an-dr-eas-k/the-alarm-clock/src/core/infrastructure/rpi_gpio.py

from concurrent.futures import ThreadPoolExecutor
import logging
import threading
from core.infrastructure.event_bus import EventBus
from core.infrastructure.events_infrastructure import (
    ButtonDirection,
    DeviceName,
    HwButtonEvent,
    HwButtonLongPressEvent,
    HwRotaryEvent,
    RotaryDirection,
)

LONG_PRESS_DURATION: float = 1.5  # seconds

logger = logging.getLogger("tac.core.infrastructure.rpi_gpio")

rotary_encoder_press_gpio: int = 5
rotary_encoder_a_gpio: int = 6
rotary_encoder_b_gpio: int = 13
mode_button_gpio: int = 12
invoke_button_gpio: int = 1


class RPiGPIOManager:

    executor: ThreadPoolExecutor
    gpio_callbacks = {}

    @property
    def _gpio_module(self):
        from RPi import GPIO  # type: ignore

        return GPIO

    def __init__(self, executor: ThreadPoolExecutor):
        self.executor = executor
        self.gpio_callbacks = {}

    def add_callback(self, pin_num, callback):
        self.gpio_callbacks[pin_num] = callback

    def setup(self):
        self._gpio_module.setmode(self._gpio_module.BCM)
        configured_pins = self.gpio_callbacks.keys()
        logger.info(f"Configuring gpio pins: {configured_pins}")

        for pin in configured_pins:
            self._gpio_module.setup(
                pin, self._gpio_module.IN, pull_up_down=self._gpio_module.PUD_UP
            )

            self._gpio_module.add_event_detect(
                pin,
                self._gpio_module.BOTH,
                callback=self.callback_wrapper,
                bouncetime=2,
            )

    def callback_wrapper(self, channel):
        all_pin_values = self.read_all_pins()
        logger.debug(
            f"GPIO event detected on channel {channel}, pin values: {all_pin_values}"
        )
        self.executor.submit(
            self.gpio_callbacks[channel],
            bool(all_pin_values[channel]),
            all_pin_values,
        )

    def read_all_pins(self):
        pin_values = {}
        for pin in self.gpio_callbacks.keys():
            pin_values[pin] = int(self._gpio_module.input(pin))
        return pin_values

    def cleanup(self):
        logger.info("Cleaning up GPIO")
        self._gpio_module.cleanup()


class GPIOInputManager:
    last_states = [(0, 0), (0, 0)]

    def __init__(self, gpio_manager: RPiGPIOManager, event_bus: EventBus = None):
        super().__init__()
        self.gpio_manager = gpio_manager
        self.event_bus = event_bus
        self._long_press_timers: dict[DeviceName, threading.Timer] = {}

        self.gpio_manager.add_callback(mode_button_gpio, self._mode_button_callback)
        self.gpio_manager.add_callback(invoke_button_gpio, self._invoke_button_callback)
        self.gpio_manager.add_callback(
            rotary_encoder_a_gpio, self._rotary_encoder_callback
        )
        self.gpio_manager.add_callback(rotary_encoder_b_gpio, lambda v, p: {})

        self.gpio_manager.setup()

        channel_a_value = int(
            not self.gpio_manager.read_all_pins()[rotary_encoder_a_gpio]
        )
        channel_b_value = int(
            not self.gpio_manager.read_all_pins()[rotary_encoder_b_gpio]
        )

        self.last_states = [(channel_a_value, channel_b_value), (None, None)]

        logger.info(
            f"gpio initialized for buttons and rotary encoder input. Initial rotary encoder state: {self.last_states[0]}"
        )

    def _rotary_encoder_callback(self, _: bool, pin_values=None):

        channel_a_value = pin_values[rotary_encoder_a_gpio]

        channel_b_value = pin_values[rotary_encoder_b_gpio]
        state = (channel_a_value, channel_b_value)
        logger.debug(
            f"Rotary encoder current state: {state}, last state: {self.last_states[0]}"
        )

        if channel_b_value != channel_a_value:
            logger.debug(
                f"Rotary clockwise detected, {'1st tick' if channel_a_value == 1 else 'later tick'}"
            )

            self.event_bus.emit(
                HwRotaryEvent(
                    DeviceName.ROTARY_ENCODER,
                    RotaryDirection.CLOCKWISE,
                    channel_a_value == 1,
                )
            )
        else:
            logger.debug(
                f"Rotary counter-clockwise detected, {'1st tick' if channel_a_value == 0 else 'later tick'}"
            )
            self.event_bus.emit(
                HwRotaryEvent(
                    DeviceName.ROTARY_ENCODER,
                    RotaryDirection.COUNTERCLOCKWISE,
                    channel_a_value == 0,
                )
            )

        self.last_states[1] = self.last_states[0]
        self.last_states[0] = state

    def _start_long_press_timer(self, device_name: DeviceName):
        self._cancel_long_press_timer(device_name)
        t = threading.Timer(
            LONG_PRESS_DURATION, self._emit_long_press, args=[device_name]
        )
        self._long_press_timers[device_name] = t
        t.start()

    def _cancel_long_press_timer(self, device_name: DeviceName):
        timer = self._long_press_timers.pop(device_name, None)
        if timer:
            timer.cancel()

    def _emit_long_press(self, device_name: DeviceName):
        self._long_press_timers.pop(device_name, None)
        logger.debug(f"Long press detected on {device_name}")
        self.event_bus.emit(HwButtonLongPressEvent(device_name=device_name))

    def _mode_button_callback(self, pin_value: bool, _=None):
        logger.debug("Mode button state changed")
        direction = ButtonDirection.DOWN if not pin_value else ButtonDirection.UP
        if direction == ButtonDirection.DOWN:
            self._start_long_press_timer(DeviceName.MODE_BUTTON)
        else:
            self._cancel_long_press_timer(DeviceName.MODE_BUTTON)
        self.event_bus.emit(
            HwButtonEvent(device_name=DeviceName.MODE_BUTTON, direction=direction)
        )

    def _invoke_button_callback(self, pin_value: bool, _=None):
        logger.debug("Invoke button state changed")
        direction = ButtonDirection.DOWN if not pin_value else ButtonDirection.UP
        if direction == ButtonDirection.DOWN:
            self._start_long_press_timer(DeviceName.INVOKE_BUTTON)
        else:
            self._cancel_long_press_timer(DeviceName.INVOKE_BUTTON)
        self.event_bus.emit(
            HwButtonEvent(device_name=DeviceName.INVOKE_BUTTON, direction=direction)
        )
