an-dr-eas-k/the-alarm-clock/src/core/application/system_service.py

import datetime
import logging
import threading
import traceback
from core.domain.events import (
    ForcedDisplayUpdateEvent,
    PlaybackChangedEvent,
    PreAlarmTriggeredEvent,
    ShutdownSystemRequest,
    SpotifyStoppedEvent,
    StartupFinishedEvent,
    SunEventOccurredEvent,
    TerminateAppRequest,
    VolumeChangedEvent,
    WeatherUpdatedEvent,
    WifiStatusChangedEvent,
    AlarmTriggeredEvent,
    AlarmStoppedEvent,
)
from core.domain.model import (
    AlarmClockContext,
    Mode,
    RoomBrightness,
    SchedulerJobIds,
)
from core.infrastructure.brightness_sensor import IBrightnessSensor
from core.infrastructure.event_bus import EventBus
from core.infrastructure.scheduler import SchedulerService, SchedulerStores
from core.interface.display.display_content import DisplayContent
from utils.geolocation import GeoLocation, SunEvent
from utils.os_interactions import OSInteraction

from utils.memory_profiler import print_full_report

logger = logging.getLogger("tac.core.application.system_service")


def safe_action(
    action, info_msg: str = None, debug_msg: str = None, logger: logging.Logger = None
):
    try:
        if logger:
            if debug_msg:
                logger.debug(debug_msg)
            if info_msg:
                logger.info(info_msg)
        else:
            raise ValueError("logger must be provided to safe_action")
        action()
    except:
        logger.error("%s", traceback.format_exc())


class SystemService:
    _previous_tac_time = GeoLocation().now()

    def __init__(
        self,
        alarm_clock_context: AlarmClockContext,
        scheduler_service: SchedulerService,
        event_bus: EventBus,
        display_content: DisplayContent,
        brightness_sensor: IBrightnessSensor,
        os_interaction: OSInteraction,
    ):
        self.alarm_clock_context = alarm_clock_context
        self.scheduler_service = scheduler_service
        self.event_bus = event_bus
        self.display_content = display_content
        self.brightness_sensor = brightness_sensor
        self.os_interaction = os_interaction

        self.event_bus.on(WifiStatusChangedEvent)(self.handle_wifi_status_changed)
        self.event_bus.on(AlarmTriggeredEvent)(self.handle_alarm_triggered)
        self.event_bus.on(AlarmStoppedEvent)(self.handle_alarm_stopped)
        self.event_bus.on(SpotifyStoppedEvent)(self.handle_spotify_stopped)
        self.event_bus.on(VolumeChangedEvent)(self._volume_changed)
        self.event_bus.on(ForcedDisplayUpdateEvent)(self.handle_forced_display_update)
        self.event_bus.on(TerminateAppRequest)(self.handle_terminate_request)
        self.event_bus.on(ShutdownSystemRequest)(self.handle_shutdown_system_request)
        self.event_bus.on(PreAlarmTriggeredEvent)(self.handle_pre_alarm_triggered)
        self.event_bus.on(StartupFinishedEvent)(self.handle_startup_finished)

        self._update_weather_status()
        self._add_scheduler_jobs()
        self.scheduler_service.log_active_jobs(SchedulerStores.default.value)

    def _add_scheduler_jobs(self):
        self.scheduler_service.add_job(
            self._emit_regular_display_update,
            trigger="interval",
            start_date=datetime.date.today(),
            seconds=self.alarm_clock_context.config.refresh_timeout_in_secs,
            job_id=SchedulerJobIds.regular_display_refresh.value,
            jobstore=SchedulerStores.default.value,
        )

        self.scheduler_service.add_job(
            self._update_wifi_status,
            trigger="interval",
            seconds=60,
            job_id=SchedulerJobIds.wifi_check.value,
            jobstore=SchedulerStores.default.value,
        )

        self.scheduler_service.add_job(
            self._update_weather_status,
            trigger="interval",
            minutes=5,
            job_id=SchedulerJobIds.weather_update_interval.value,
            jobstore=SchedulerStores.default.value,
        )

        for event in SunEvent.__members__.values():
            self.init_sun_event_scheduler(event)

    def init_sun_event_scheduler(self, event: SunEvent):
        self.scheduler_service.add_cron_job(
            lambda: self._sun_event_occured(event),
            job_id=event.value,
            jobstore=SchedulerStores.default.value,
            **self.alarm_clock_context.environment.geo_location.get_sun_event_cron_args(
                event
            ),
        )

    def handle_alarm_triggered(self, _: AlarmTriggeredEvent):
        pass

    def handle_spotify_stopped(self, _: SpotifyStoppedEvent):
        self.os_interaction.restart_spotify_daemon()

    def _volume_changed(self, _: VolumeChangedEvent):
        self.start_hide_volume_meter_trigger()

    def start_hide_volume_meter_trigger(self):
        self.scheduler_service.start_generic_trigger(
            SchedulerJobIds.hide_volume_meter.value,
            datetime.timedelta(seconds=5),
            func=self.display_content.hide_volume_meter,
        )

    def handle_alarm_stopped(self, _: AlarmStoppedEvent):
        pass

    def handle_wifi_status_changed(self, event: WifiStatusChangedEvent):
        self.alarm_clock_context.environment.is_online = event.is_online
        if event.is_online:
            self._update_weather_status()

    def handle_forced_display_update(self, _: ForcedDisplayUpdateEvent):
        self._previous_tac_time = GeoLocation().now()
        pass

    def handle_startup_finished(self, _: StartupFinishedEvent):
        self._update_wifi_status()

    def handle_pre_alarm_triggered(self, _: PreAlarmTriggeredEvent):
        if not self.alarm_clock_context.environment.is_online:
            self.os_interaction.restart_networking_service()

    def handle_shutdown_system_request(self, event: ShutdownSystemRequest):
        def do():
            if event.reboot:
                self.os_interaction.reboot_system()
            else:
                self.os_interaction.shutdown_system()

        safe_action(do, "shutting down system", logger=logger)

    def handle_terminate_request(self, _: TerminateAppRequest):
        def do():
            for thread in threading.enumerate():
                logger.info("Thread: %s", thread)
            self.event_bus.emit(PlaybackChangedEvent(playback_mode=Mode.Idle))
            # self.scheduler_service.shutdown()
            self.event_bus.clear()

            logger.info("application shutdown completed.")

        safe_action(do, "terminating application", logger=logger)

    def _update_weather_status(self):
        def do():

            new_weather = None

            if self.alarm_clock_context.environment.is_online:
                new_weather = GeoLocation().get_current_weather()

            if new_weather == self.alarm_clock_context.environment.current_weather:
                return

            logger.info("weather updating: %s", new_weather)
            self.alarm_clock_context.environment.current_weather = new_weather
            self.event_bus.emit(WeatherUpdatedEvent(weather=new_weather))

        safe_action(do, "updating weather status", logger=logger)

    def _update_wifi_status(self):
        def do():
            is_online = self.os_interaction.is_internet_available()

            if is_online == self.alarm_clock_context.environment.is_online:
                return

            logger.info("change wifi state, is online: %s", is_online)
            self.event_bus.emit(WifiStatusChangedEvent(is_online))

        safe_action(do, "updating wifi status", logger=logger)

    def _sun_event_occured(self, event: SunEvent):
        def do():
            self.event_bus.emit(SunEventOccurredEvent(event))
            self.alarm_clock_context.environment.is_daytime = event == SunEvent.sunrise
            self.init_sun_event_scheduler(event)

        safe_action(do, "sun event %s" % event, logger=logger)

    def _emit_regular_display_update(self):
        def do():
            tac_time = GeoLocation().now()
            new_blink_state = self.display_content.show_blink_segment

            if self._previous_tac_time.second != tac_time.second:
                new_blink_state = not self.display_content.show_blink_segment
                self._previous_tac_time = tac_time

            if self.display_content.update_presentation_state(
                show_blink_segment=new_blink_state,
                room_brightness=RoomBrightness(self.get_room_brightness()),
            ):
                self.event_bus.emit(
                    ForcedDisplayUpdateEvent(
                        suppress_logging=True,
                    )
                )
                self.display_content.refresh_duration_in_ms = int(
                    (GeoLocation().now() - tac_time).total_seconds() * 1000
                )

        safe_action(do, debug_msg="regular display update", logger=logger)

    def get_room_brightness(self):
        return self.brightness_sensor.get_room_brightness()
