an-dr-eas-k/the-alarm-clock/rpi/resources/rpi-boot-config.txt

dtparam=i2c_arm=on
#dtparam=i2s=on
dtparam=spi=on

auto_initramfs=1

disable_fw_kms_setup=1

disable_overscan=1

arm_boost=1

[cm4]
otg_mode=1

[all]
dtoverlay=
dtoverlay=rpi-digiampplus,auto_mute_amp
dtparam=sd_poll_once
